sezgynus/g11-battery-protocol-emulation/ASSETS/all_graphs.png

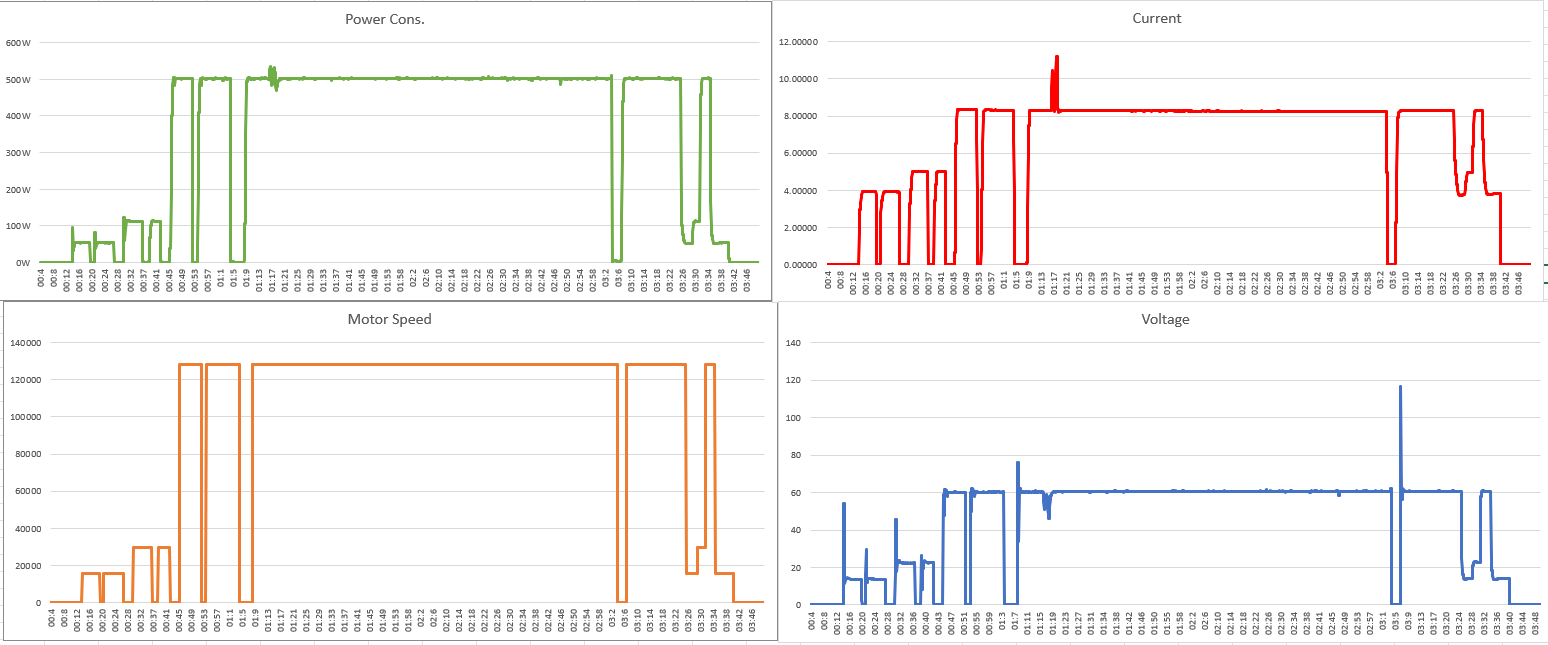
ASSETS/all_graphs.png
